Archive-663/CZ82/ASSETS/PHOTO/1 (1).jpg

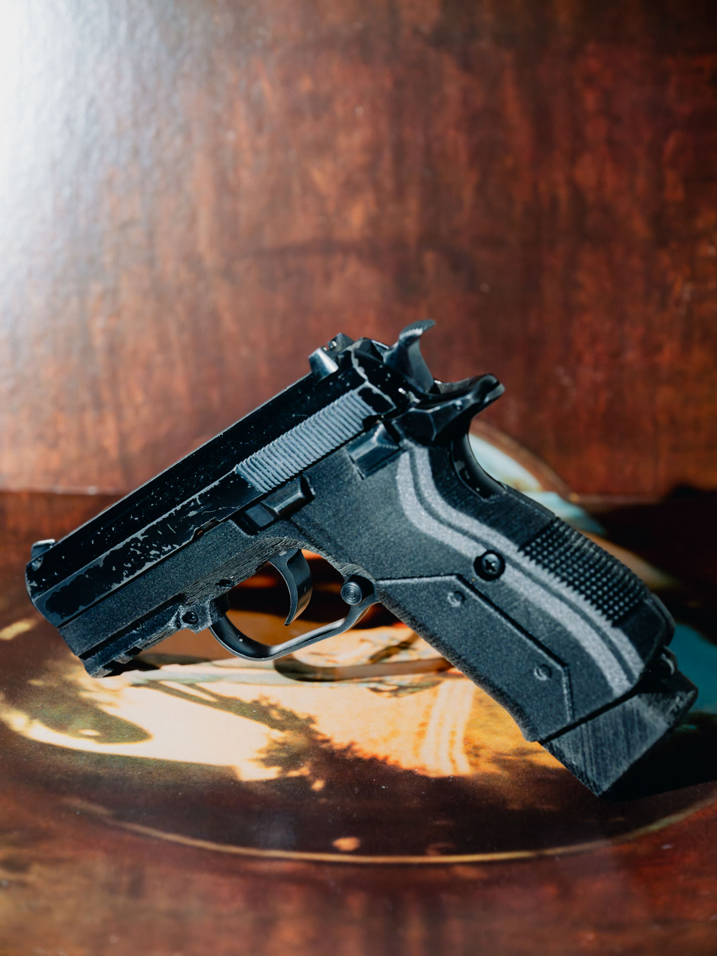
ASSETS/PHOTO/1 (1).jpg
