Archive-663/CZ82/ASSETS/PHOTO/cz (12).jpg

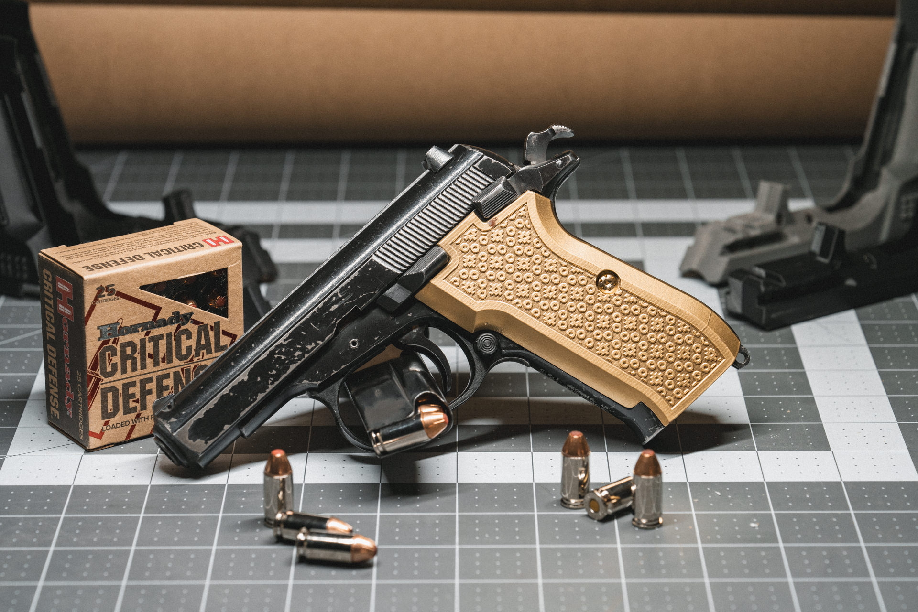
ASSETS/PHOTO/cz (12).jpg
