Archive-663/CZ82/ASSETS/PHOTO/cz (14).jpg

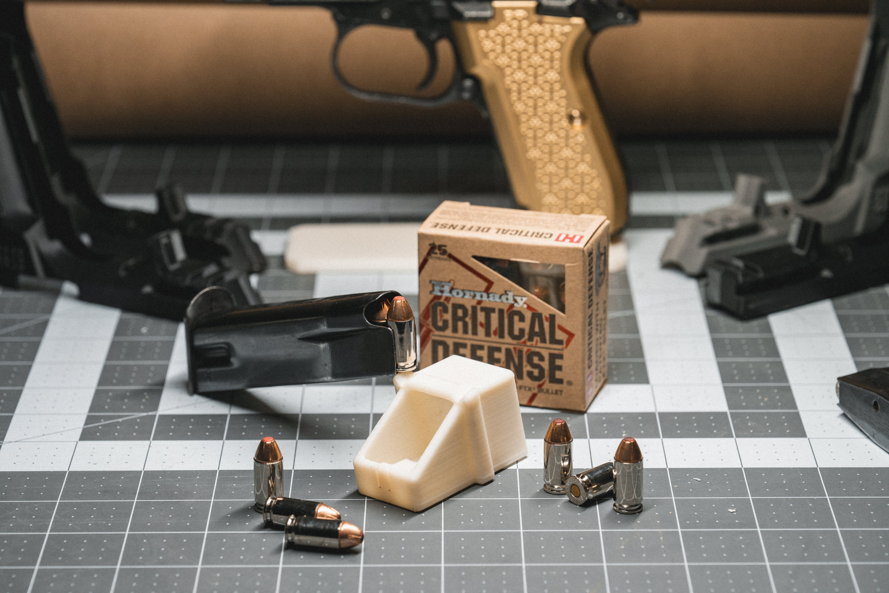
ASSETS/PHOTO/cz (14).jpg
