Archive-663/CZ82/ASSETS/PHOTO/cz (15).jpg

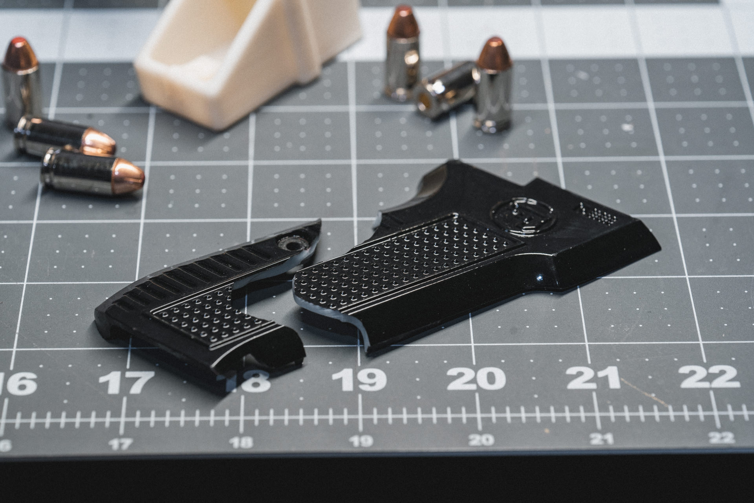
ASSETS/PHOTO/cz (15).jpg
