Archive-663/CZ82/ASSETS/PHOTO/cz (16).jpg

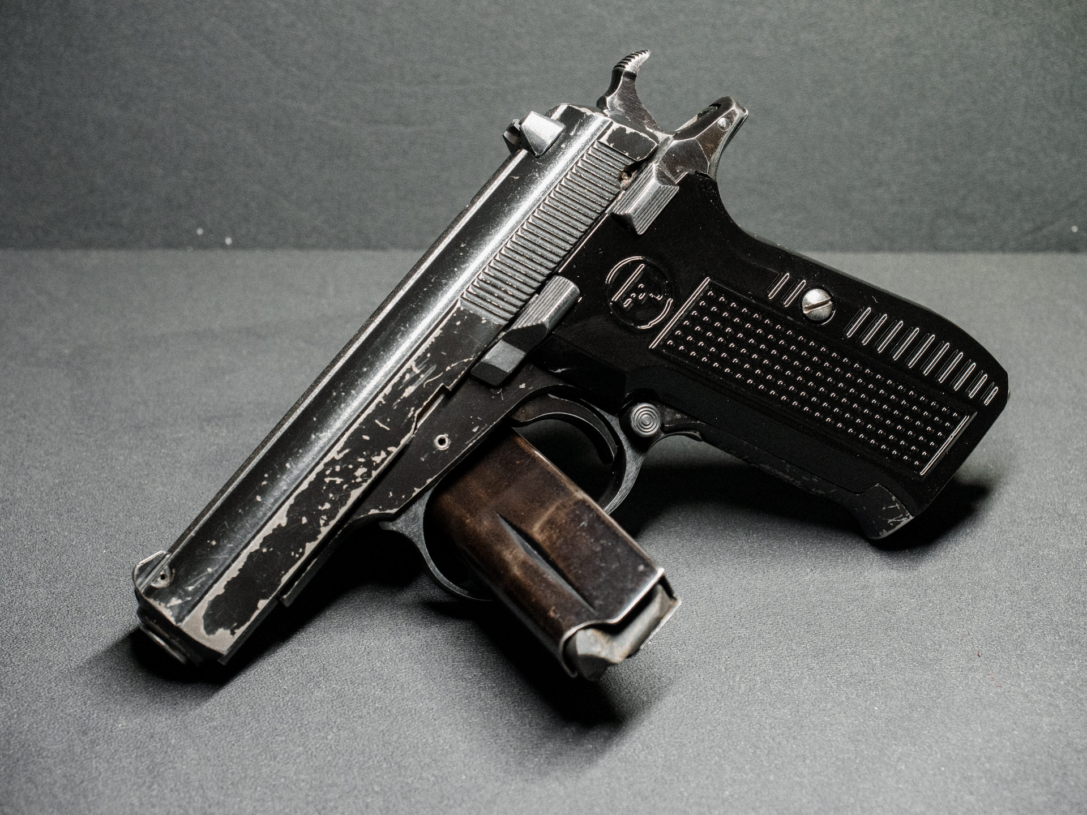
ASSETS/PHOTO/cz (16).jpg
