Archive-663/CZ82/ASSETS/PHOTO/INSTA/INSTA-01.jpg

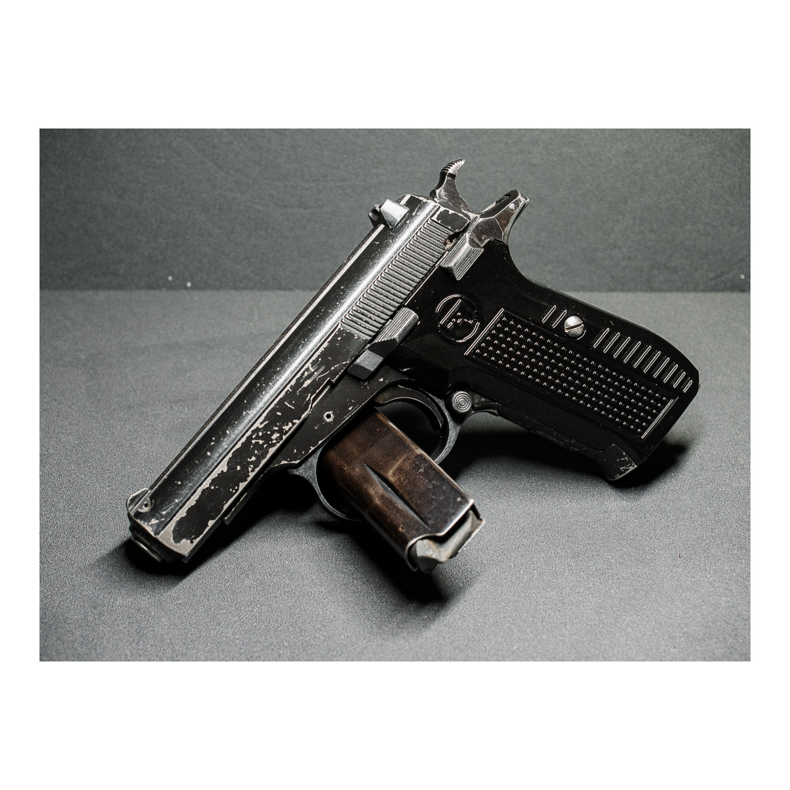
ASSETS/PHOTO/INSTA/INSTA-01.jpg
