Archive-663/CZ82/ASSETS/PHOTO/INSTA/INSTA-04.jpg

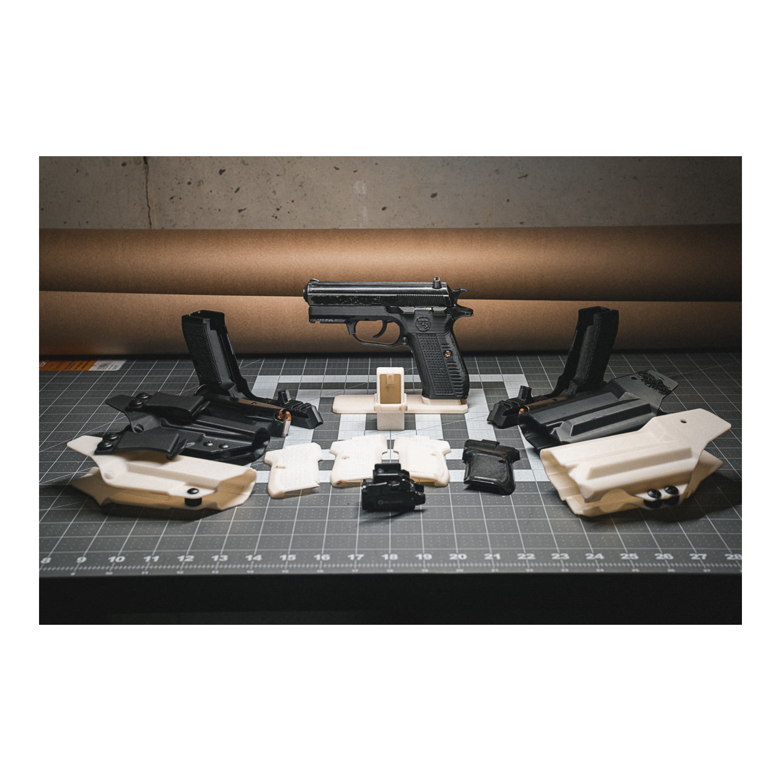
ASSETS/PHOTO/INSTA/INSTA-04.jpg
