Archive-663/CZ82/ASSETS/PHOTO/INSTA/INSTA-08.jpg

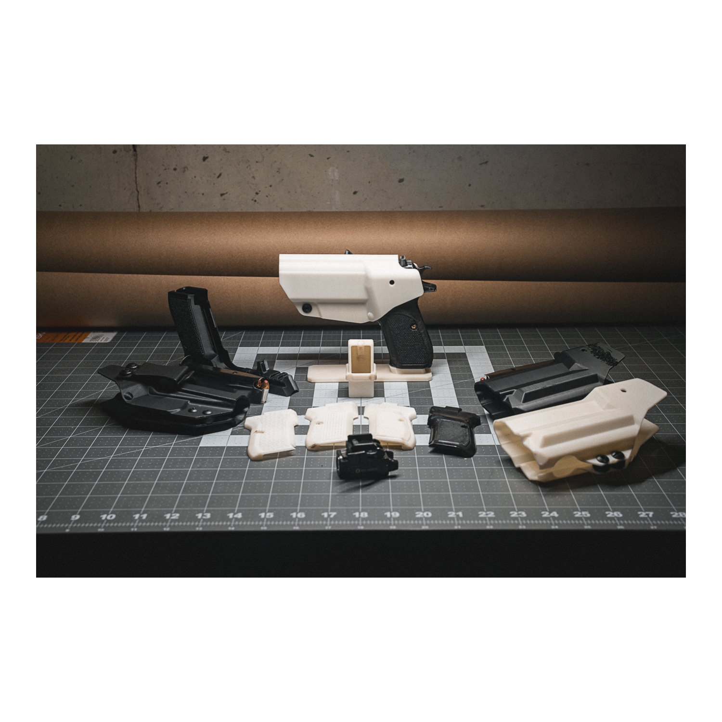
ASSETS/PHOTO/INSTA/INSTA-08.jpg
