Archive-663/CZ82/ASSETS/PHOTO/INSTA/INSTA-15.jpg

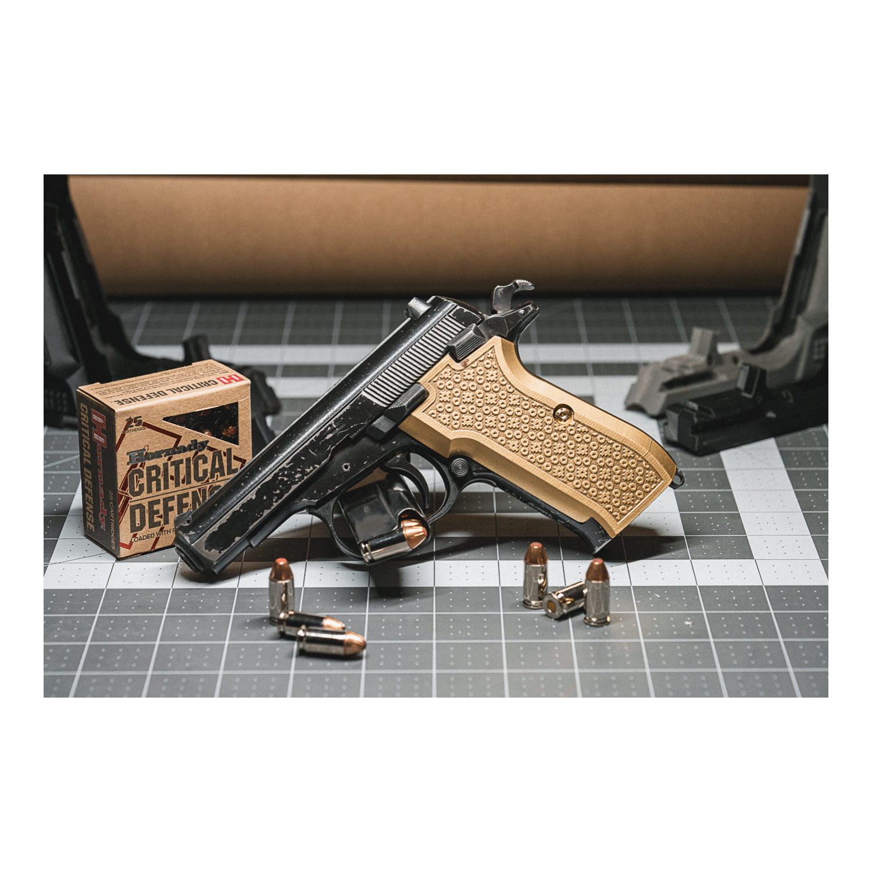
ASSETS/PHOTO/INSTA/INSTA-15.jpg
