Archive-663/CZ82/ASSETS/PHOTO/INSTA/INSTA-16.jpg

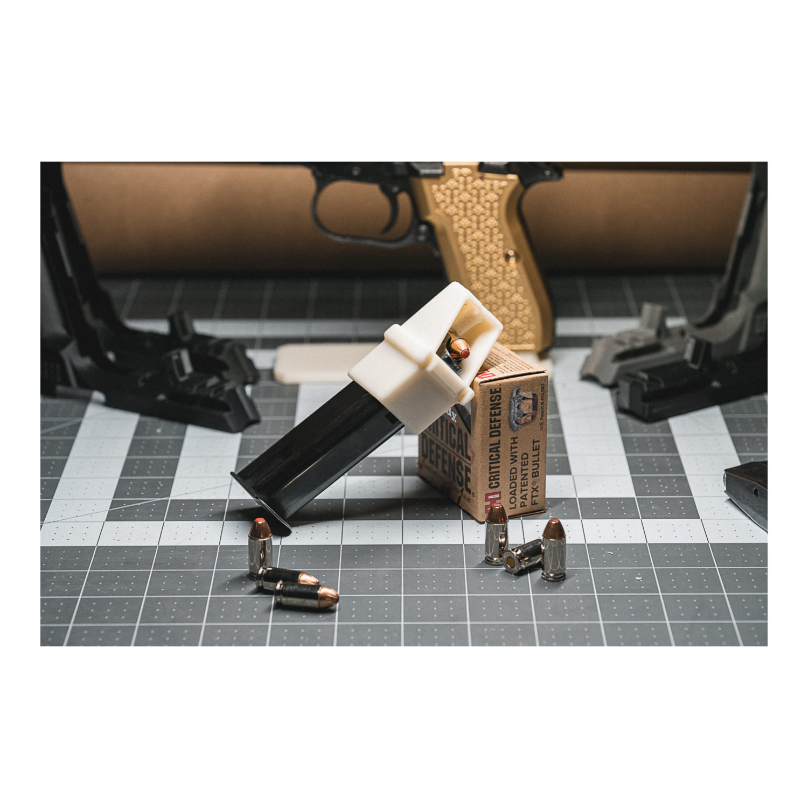
ASSETS/PHOTO/INSTA/INSTA-16.jpg
