Archive-663/CZ82/ASSETS/PHOTO/INSTA/INSTA-17.jpg

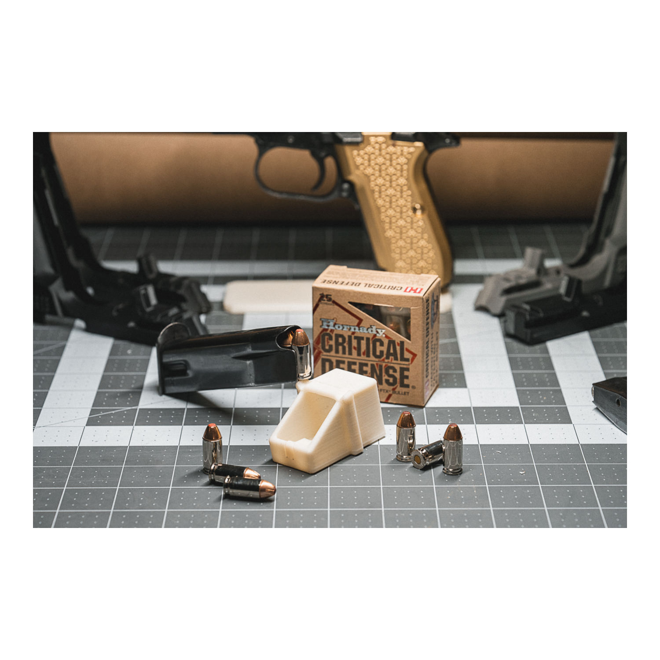
ASSETS/PHOTO/INSTA/INSTA-17.jpg
