Archive-663/CZ82/ASSETS/PHOTO/sqTG (2).jpg

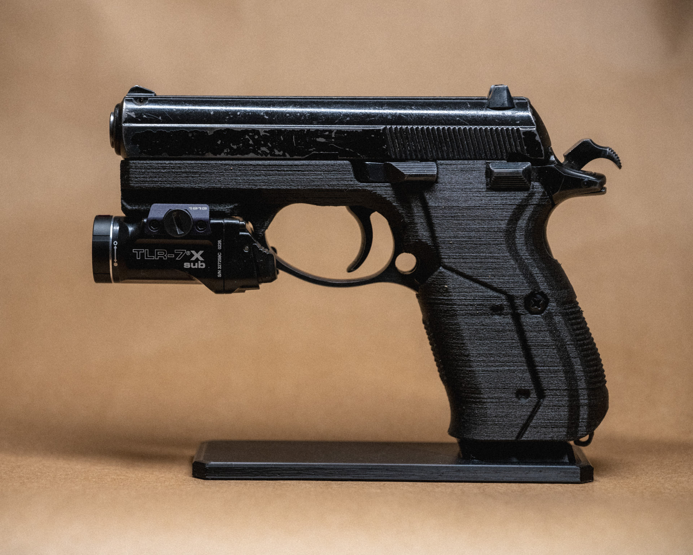
ASSETS/PHOTO/sqTG (2).jpg
