Archive-663/CZ82/ASSETS/screenGrabs/CZ82_speedLoader.jpg

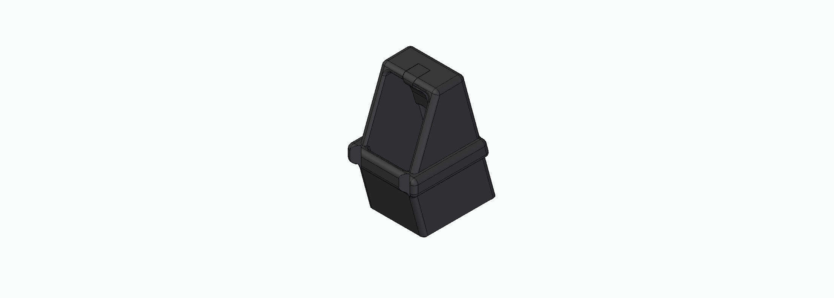
ASSETS/screenGrabs/CZ82_speedLoader.jpg
