Archive-663/CZ82/Speedloader/STL/CZ82_speedLoader_printOrientationFile.3mf

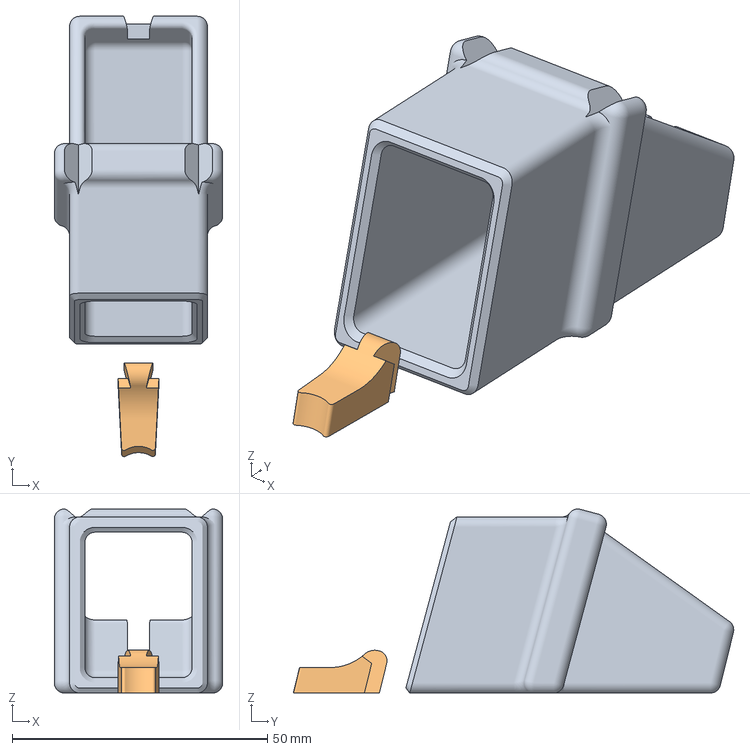
[picture p46: CAD file, 2023-09-18]
Speedloader/STL/CZ82_speedLoader_printOrientationFile.3mf
33.0 x 86.3 x 36.1 mm
CZ82_speedLoader_mainBody.stl
CZ82_speedLoader_plunger.stl
