Archive-663/CZ82/baseCZ82_Body/CZ82_baseBody.stp

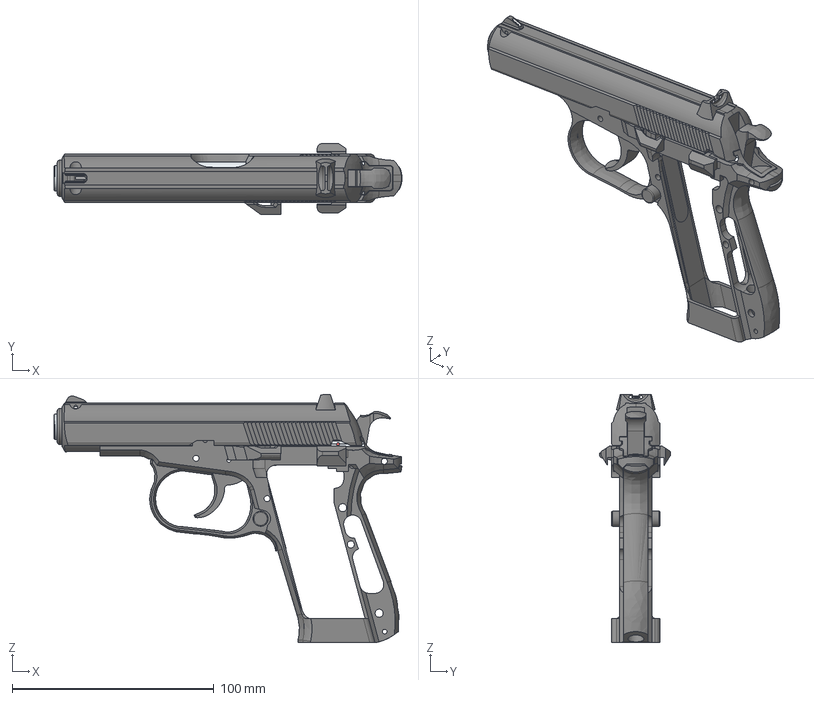
[picture p47: CAD file, 2023-09-18]
baseCZ82_Body/CZ82_baseBody.stp
172.7 x 35.2 x 123.3 mm
CZ82_baseSlide
CZ82_baseTrigger
CZ82_baseTriggerGuard
CZ82_baseFrontSight
CZ82_baseRearSight
CZ82_baseSlideLock
CZ82_baseFrame
CZ82_baseMagazineRelease
CZ82_baseSaftey
CZ82_baseHammer
CZ82_baseEjector
