Archive-663/CZ82/Grips/STEP/NATO_Bebop/CZ82_standardGripLeft_NATO_bebop_checkering_squareTGa.stp

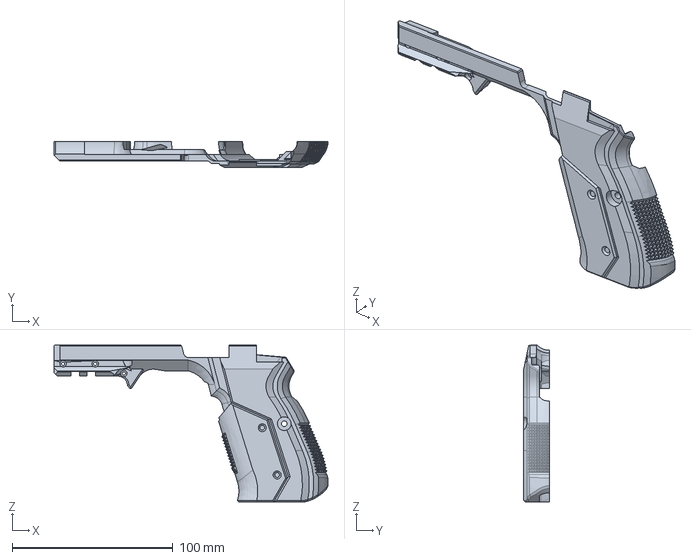
[picture p48: CAD file, 2026-04-01]
Grips/STEP/NATO_Bebop/CZ82_standardGripLeft_NATO_bebop_checkering_squareTGa.stp
170.7 x 16.0 x 97.8 mm
