Archive-663/CZ82/Grips/STEP/Slim_Bebop/CZ82_standardGripRight_Slim_bebop_checkering.stp

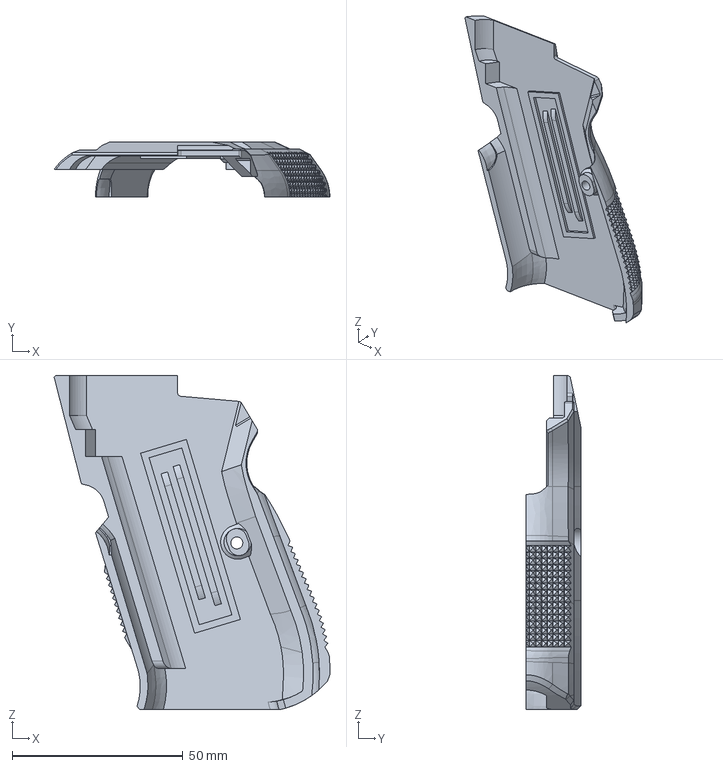
[picture p49: CAD file, 2026-03-04]
Grips/STEP/Slim_Bebop/CZ82_standardGripRight_Slim_bebop_checkering.stp
80.7 x 16.0 x 97.8 mm
