Archive-663/CZ82/Grips/STL/Slim_28mm/Elephants Foot Pattern Grip/CZ82_standardGripRight_28mm.stl

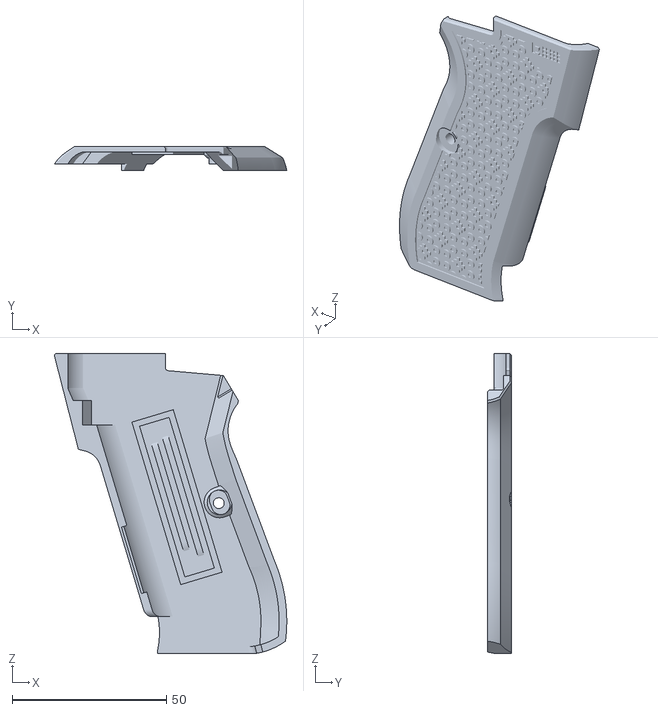
[picture p50: CAD file, 2023-09-18]
Grips/STL/Slim_28mm/Elephants Foot Pattern Grip/CZ82_standardGripRight_28mm.stl
75.4 x 7.70 x 97.2
