Archive-663/CZ82/Grips/STL/Standard_34mm/CZ82_standardGripRight_34mm.stl

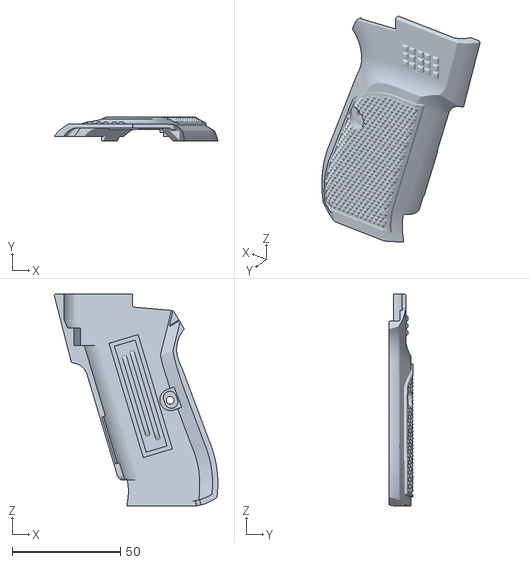
[picture p51: CAD file, 2023-09-18]
Grips/STL/Standard_34mm/CZ82_standardGripRight_34mm.stl
75.5 x 11.0 x 97.7
