Archive-663/CZ82/Holsters/STEP/CZ82_olightNATO_Slim_Holster.stp

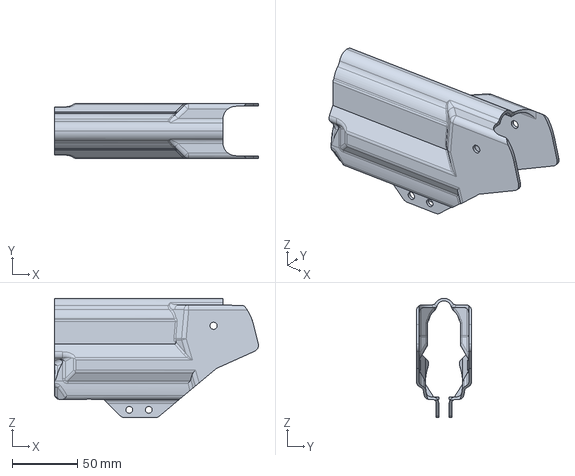
[picture p52: CAD file, 2023-09-18]
Holsters/STEP/CZ82_olightNATO_Slim_Holster.stp
156.8 x 42.1 x 91.7 mm
