Archive-663/CZ82/Holsters/STL/CZ82_baseMagazineHolster_printOrientationFile.3mf

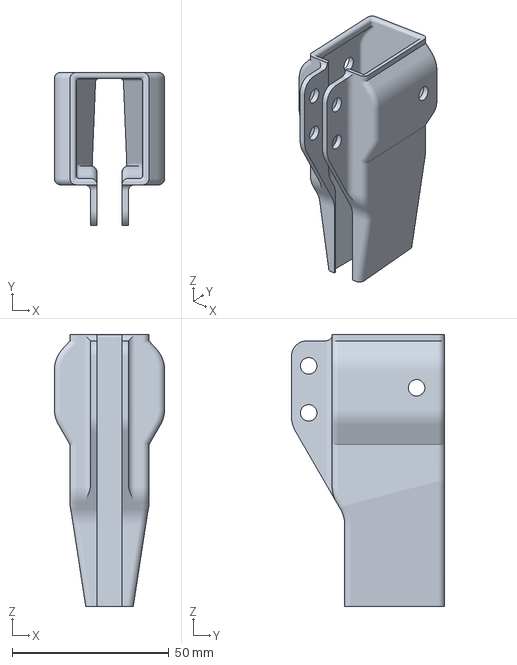
[picture p53: CAD file, 2023-09-18]
Holsters/STL/CZ82_baseMagazineHolster_printOrientationFile.3mf
35.2 x 48.9 x 86.8 mm
