Archive-663/CZ82/Lights/STEP/olight_PL_MINI2/oLight_PL_MINI2_lightModule.stp

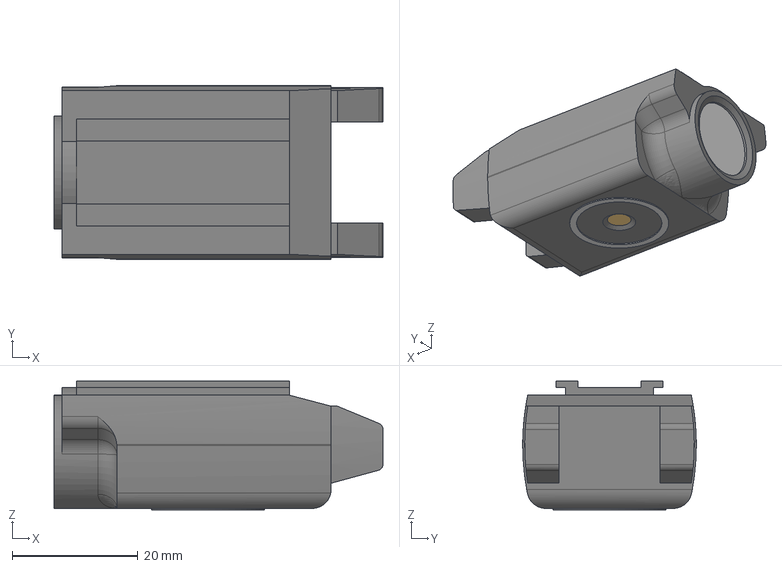
[picture p54: CAD file, 2023-09-18]
Lights/STEP/olight_PL_MINI2/oLight_PL_MINI2_lightModule.stp
52.3 x 27.6 x 20.5 mm
