Archive-663/CZ82/Magazine Base Plate/STEP/CZ82_magazineExtension_springRetainer_+2.stp

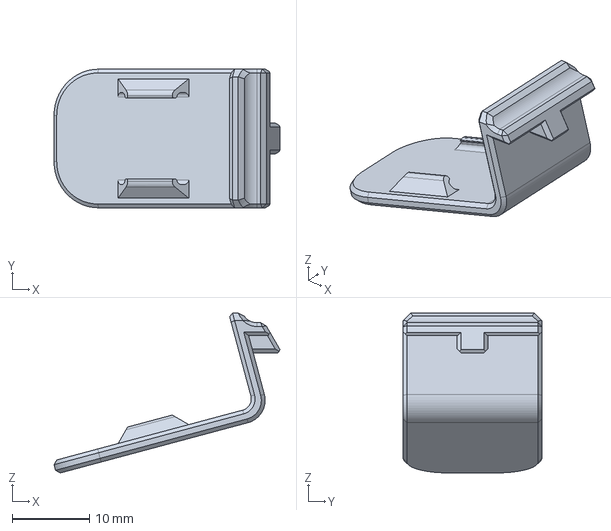
[picture p55: CAD file, 2026-03-05]
Magazine Base Plate/STEP/CZ82_magazineExtension_springRetainer_+2.stp
29.3 x 18.0 x 20.8 mm
