Archive-663/CZ82/Magazine Base Plate/STL/CZ82_magazineExtension_+2_printOrientation.3mf

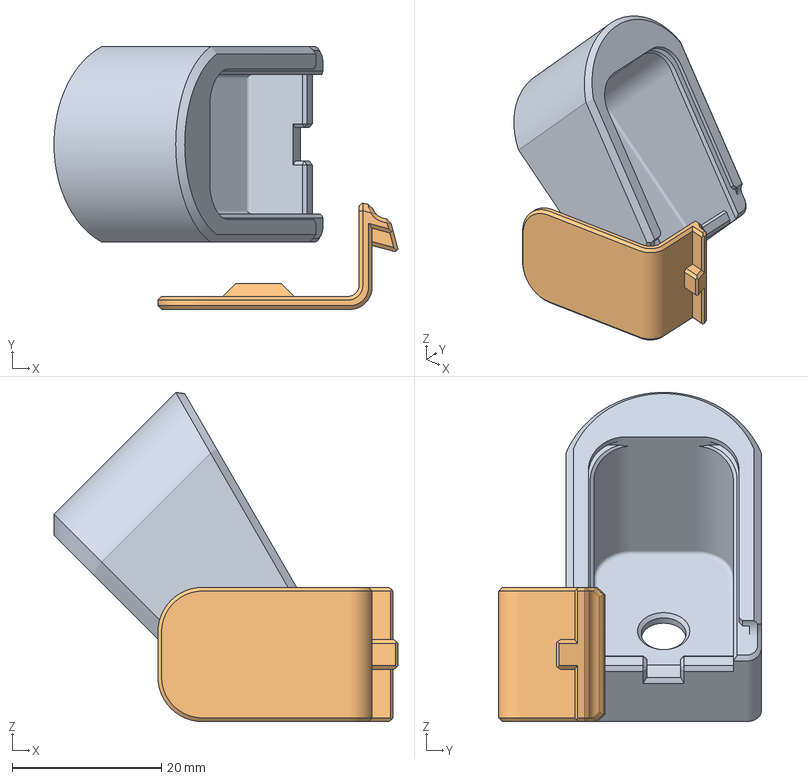
[picture p56: CAD file, 2026-03-05]
Magazine Base Plate/STL/CZ82_magazineExtension_+2_printOrientation.3mf
46.1 x 35.2 x 44.1 mm
CZ82_magazineExtension_+2.stl
CZ82_magazineExtension_springRetainer_+2.stl
