Archive-663/CZ82/Grips/STEP/CZ82_standardGripLeft_Retro_28mm.stp

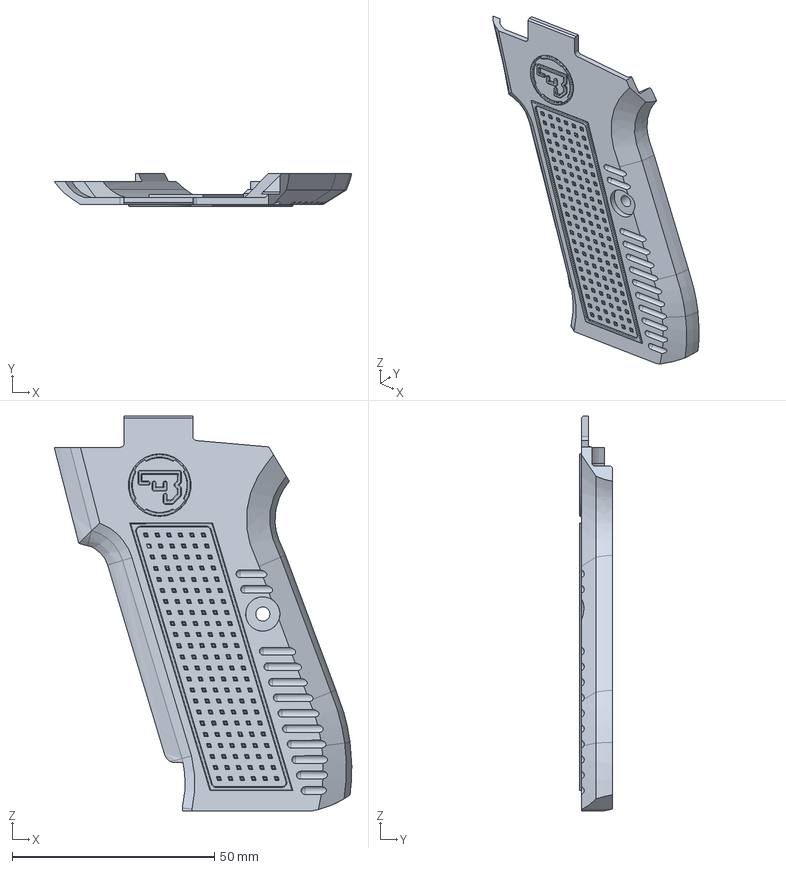
[picture p57: CAD file, 2023-09-18]
Grips/STEP/CZ82_standardGripLeft_Retro_28mm.stp
73.7 x 8.20 x 97.7 mm
