Archive-663/CZ82/Grips/STL/Slim_28mm/Elephants Foot Pattern Grip/CZ82_standardGripLeft_28mm.stl

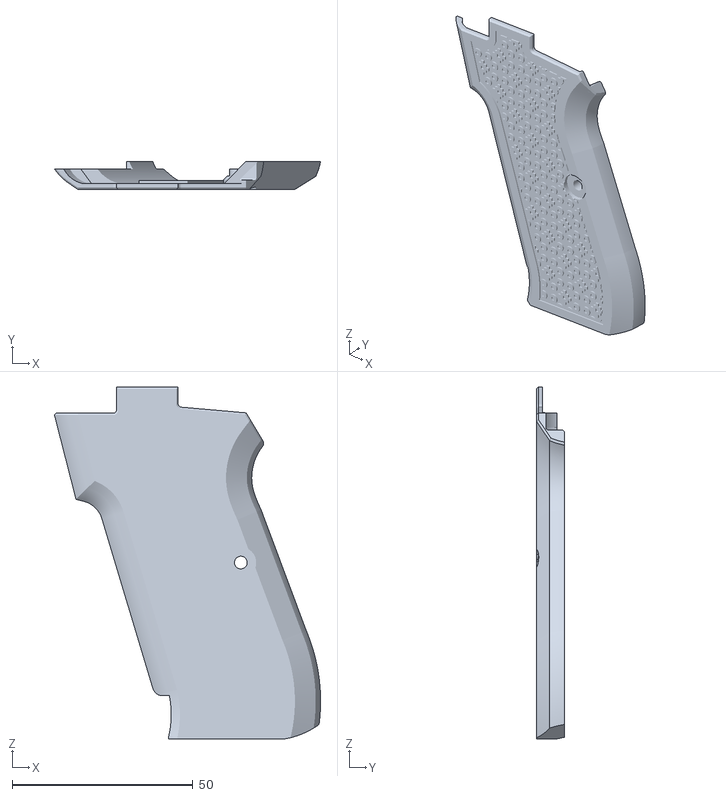
[picture p58: CAD file, 2023-09-18]
Grips/STL/Slim_28mm/Elephants Foot Pattern Grip/CZ82_standardGripLeft_28mm.stl
73.5 x 7.70 x 97.2
