Archive-663/CZ82/Grips/STL/Standard_34mm/CZ82_standardGripLeft_34mm.stl

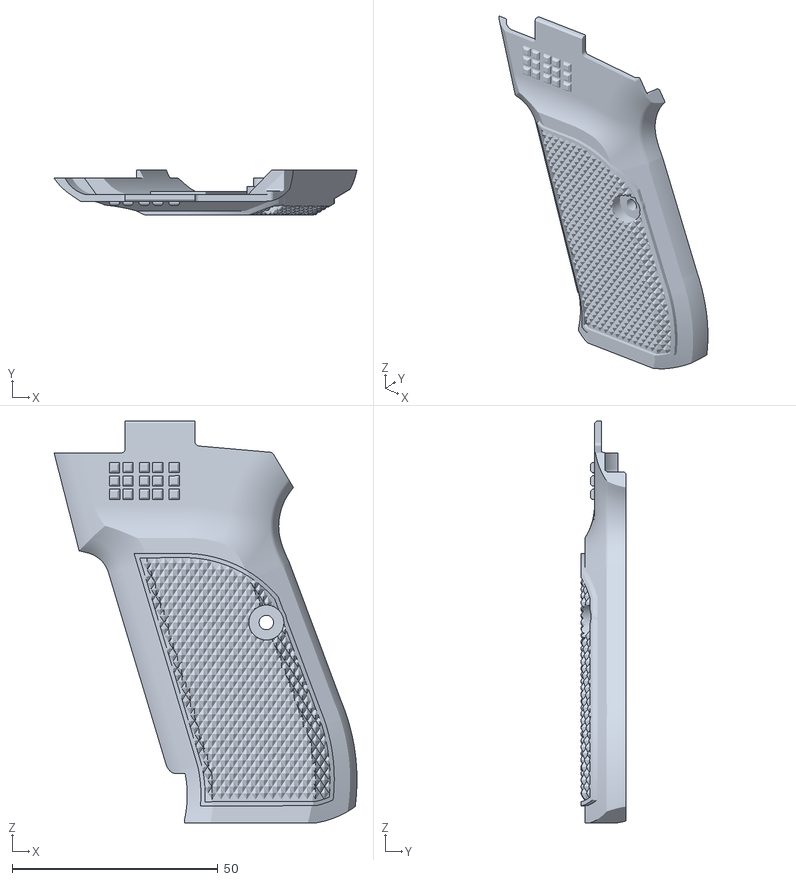
[picture p59: CAD file, 2023-09-18]
Grips/STL/Standard_34mm/CZ82_standardGripLeft_34mm.stl
73.7 x 11.0 x 97.7
