Archive-663/CZ82/Holsters/STL/CZ82_baseHolster_printOrientationFile.3mf

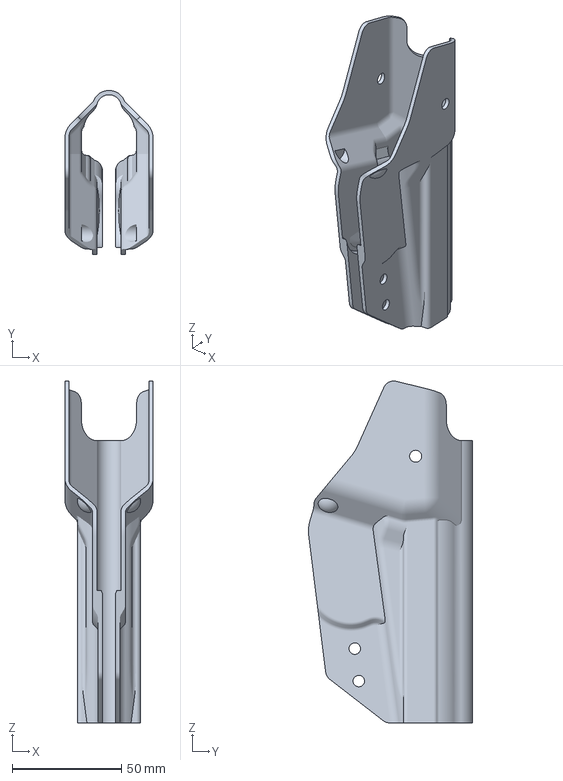
[picture p60: CAD file, 2023-09-18]
Holsters/STL/CZ82_baseHolster_printOrientationFile.3mf
40.5 x 75.2 x 156.8 mm
