Archive-663/CZ82/Grips/STEP/CZ82_standardGripRight_Retro_28mm.stp

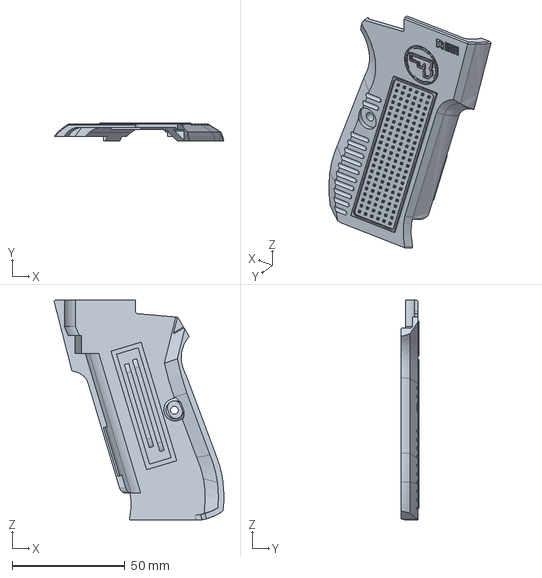
[picture p61: CAD file, 2023-09-18]
Grips/STEP/CZ82_standardGripRight_Retro_28mm.stp
75.5 x 8.20 x 97.7 mm
