Archive-663/CZ82/Grips/STEP/CZ82_standardGripLeft_Base.stp

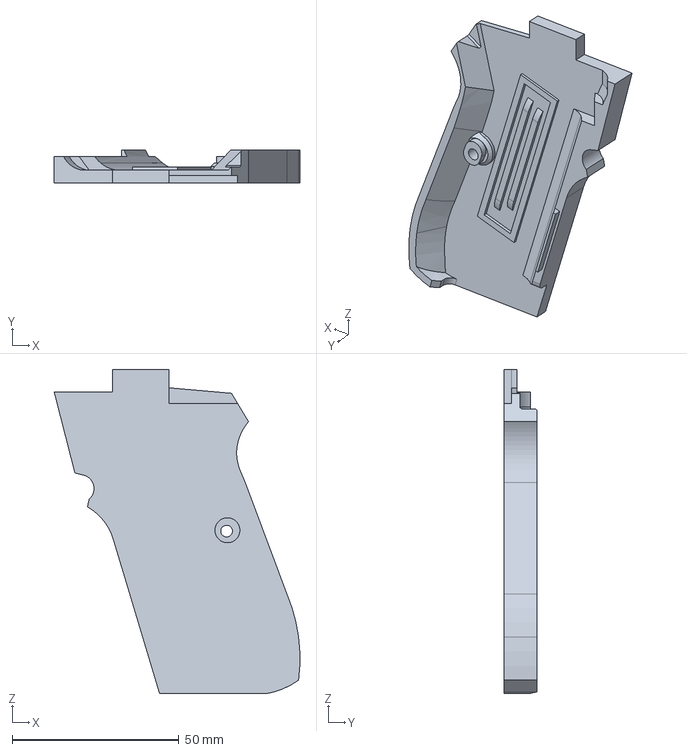
[picture p62: CAD file, 2023-09-18]
Grips/STEP/CZ82_standardGripLeft_Base.stp
73.7 x 10.0 x 97.2 mm
