Archive-663/CZ82/Grips/STEP/CZ82_standardGripLeft_28mm.stp

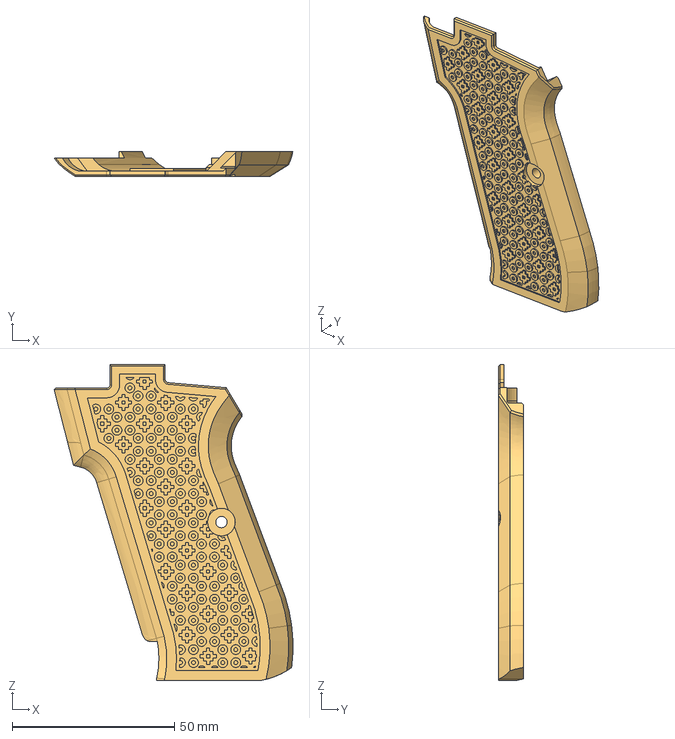
[picture p63: CAD file, 2023-09-18]
Grips/STEP/CZ82_standardGripLeft_28mm.stp
73.5 x 7.70 x 97.2 mm
